cloudmesh-community/case/cover/cover.jpg

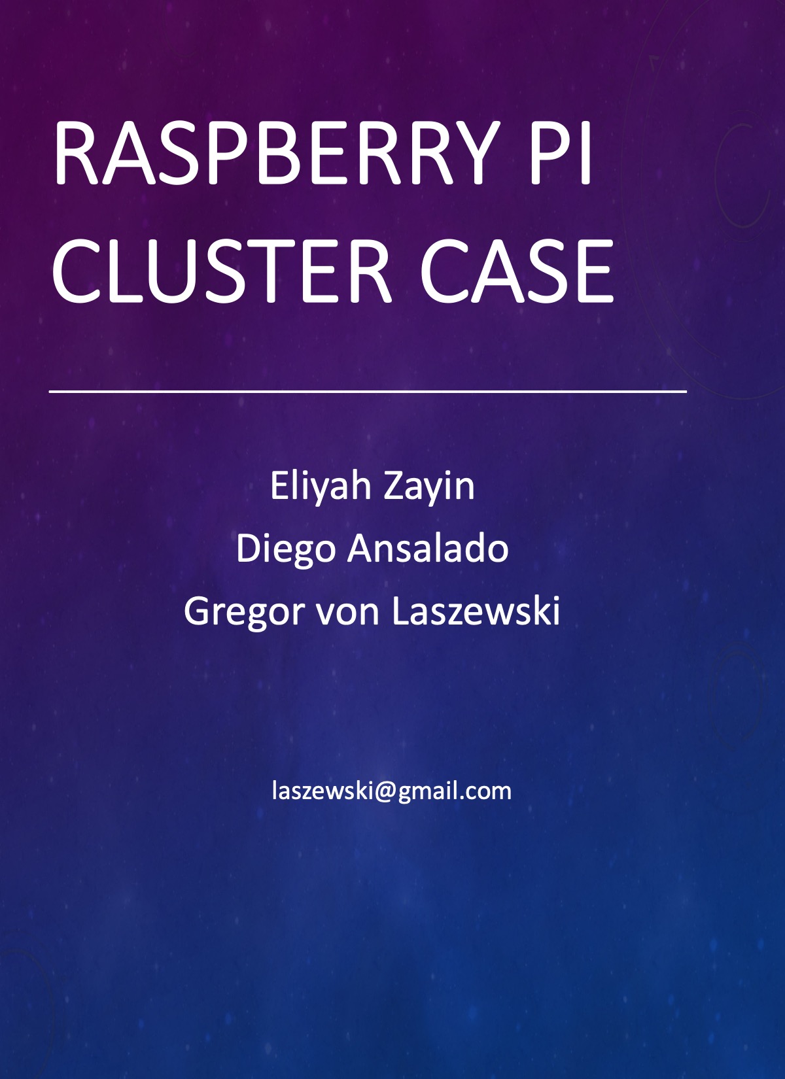
cover/cover.jpg
